NellowTCS/CL-32/Software/CL-32/include/Roboto_24.h

// Created by http://oleddisplay.squix.ch/ Consider a donation
// In case of problems make sure that you are using the font file with the correct version!
const uint8_t Roboto_24Bitmaps[] PROGMEM = {

	// Bitmap Data:
	0x00, // ' '
	0xDB,0x6D,0xB6,0xDB,0x60,0x06,0xC0, // '!'
	0x94,0xA5,0x29,0x48, // '"'
	0x06,0x30,0x18,0xC0,0x62,0x01,0x08,0x7F,0xF9,0xFF,0xE0,0xC6,0x03,0x10,0x08,0x40,0x23,0x0F,0xFF,0xBF,0xFE,0x18,0xC0,0x62,0x01,0x18,0x04,0x60,0x31,0x80, // '#'
	0x06,0x00,0x60,0x06,0x01,0xF0,0x3F,0xC7,0x0C,0x60,0xE6,0x06,0x60,0x07,0x00,0x3C,0x01,0xF8,0x03,0xC0,0x0E,0x00,0x6C,0x06,0xE0,0x67,0x0E,0x3F,0xC1,0xF8,0x06,0x00,0x60, // '$'
	0x3C,0x00,0x33,0x00,0x31,0x84,0x18,0x47,0x0C,0x22,0x06,0x33,0x01,0x99,0x00,0x79,0x80,0x01,0x80,0x00,0x9E,0x00,0xD9,0x80,0xC8,0x40,0x44,0x30,0x62,0x18,0x61,0x08,0x30,0xCC,0x00,0x3C,0x00, // '%'
	0x0F,0x00,0x7F,0x00,0xC7,0x01,0x86,0x03,0x0C,0x06,0x30,0x0F,0xC0,0x0F,0x00,0x1E,0x00,0xEE,0x31,0x8C,0x66,0x0D,0xCC,0x0F,0x1C,0x0E,0x1C,0x3C,0x3F,0xFC,0x1F,0x1C, // '&'
	0xDB,0x6D,0x80, // '''
	0x08,0x38,0x61,0x86,0x0C,0x18,0x60,0xC1,0x83,0x06,0x0C,0x18,0x30,0x60,0xC1,0x83,0x83,0x06,0x06,0x06,0x0E,0x08, // '('
	0x40,0xE0,0x30,0x30,0x18,0x18,0x0C,0x0C,0x0C,0x0C,0x0E,0x0E,0x0E,0x0E,0x0E,0x0C,0x0C,0x0C,0x0C,0x18,0x18,0x30,0x30,0x60,0xC0, // ')'
	0x0C,0x01,0x80,0x30,0x36,0xEF,0xFC,0x18,0x07,0x81,0x98,0x33,0x84,0x20, // '*'
	0x06,0x00,0x30,0x01,0x80,0x0C,0x00,0x60,0x7F,0xFB,0xFF,0xC0,0xC0,0x06,0x00,0x30,0x01,0x80,0x0C,0x00, // '+'
	0x73,0x9C,0xC6,0x60, // ','
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
	  {   769,  12,  17,  15,    2,  -17 }, // 'E'
	  {   795,  12,  17,  14,    2,  -17 }, // 'F'
	  {   821,  15,  17,  17,    1,  -17 }, // 'G'
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
};
const GFXfont Roboto_24 PROGMEM = {
(uint8_t  *)Roboto_24Bitmaps,(GFXglyph *)Roboto_24Glyphs,0x20, 0x7E, 29};
